logicallyincorrect/esp32-hid-switcher/src/HidReportMap.h

#pragma once
#include <stdint.h>
#include "PointerMode.h"
// One keyboard report ID, six keys plus modifiers. No shared live report value.
static uint8_t reportMap[] = {
  0x05,0x01, 0x09,0x06, 0xa1,0x01, 0x85,0x01,
  0x05,0x07, 0x19,0xe0, 0x29,0xe7, 0x15,0x00, 0x25,0x01,
  0x75,0x01, 0x95,0x08, 0x81,0x02,
  0x95,0x01, 0x75,0x08, 0x81,0x01,
  0x95,0x05, 0x75,0x01, 0x05,0x08, 0x19,0x01, 0x29,0x05, 0x91,0x02,
  0x95,0x01, 0x75,0x03, 0x91,0x01,
  0x95,0x06, 0x75,0x08, 0x15,0x00, 0x26,0xff,0x00,
  0x05,0x07, 0x19,0x00, 0x2a,0xff,0x00, 0x81,0x00, 0xc0,
#if HID_ABSOLUTE_POINTER
  // NanoKVM hid.GS2 layout, with report ID 2 for BLE alongside our keyboard.
  // Five buttons, absolute X/Y with explicit physical range, relative wheel.
  0x05,0x01,0x09,0x02,0xa1,0x01,0x85,0x02,0x09,0x01,0xa1,0x00,
  0x05,0x09,0x19,0x01,0x29,0x05,0x15,0x00,0x25,0x01,0x95,0x05,0x75,0x01,0x81,0x02,
  0x95,0x01,0x75,0x03,0x81,0x01,
  0x05,0x01,0x09,0x30,0x09,0x31,0x15,0x00,0x26,0xff,0x7f,0x35,0x00,0x46,0xff,0x7f,
  0x75,0x10,0x95,0x02,0x81,0x02,
  0x05,0x01,0x09,0x38,0x15,0x81,0x25,0x7f,0x35,0x00,0x45,0x00,0x75,0x08,0x95,0x01,0x81,0x06,0xc0,0xc0
#else
  // Standard relative mouse: eight buttons, signed 16-bit X/Y, wheel and pan.
  0x05,0x01,0x09,0x02,0xa1,0x01,0x85,0x02,0x09,0x01,0xa1,0x00,
  0x05,0x09,0x19,0x01,0x29,0x08,0x15,0x00,0x25,0x01,0x95,0x08,0x75,0x01,0x81,0x02,
  0x05,0x01,0x09,0x30,0x09,0x31,0x16,0x01,0x80,0x26,0xff,0x7f,0x75,0x10,0x95,0x02,0x81,0x06,
  0x09,0x38,0x15,0x81,0x25,0x7f,0x75,0x08,0x95,0x01,0x81,0x06,
  0x05,0x0c,0x0a,0x38,0x02,0x95,0x01,0x81,0x06,0xc0,0xc0
#endif
};
#if HID_ABSOLUTE_POINTER && !HID_ABSOLUTE_ONLY_TEST
// Own HID service and report map: never merge relative axes with absolute
// mouse buttons in one host HID device. Used for calibration and seamless-off.
static uint8_t relativeReportMap[] = {
  // Calibration uses a separate relative mouse; report 2 stays absolute.
  0x05,0x01,0x09,0x02,0xa1,0x01,0x85,0x03,0x09,0x01,0xa1,0x00,
  0x05,0x09,0x19,0x01,0x29,0x08,0x15,0x00,0x25,0x01,0x95,0x08,0x75,0x01,0x81,0x02,
  0x05,0x01,0x09,0x30,0x09,0x31,0x16,0x01,0x80,0x26,0xff,0x7f,0x75,0x10,0x95,0x02,0x81,0x06,
  0x09,0x38,0x15,0x81,0x25,0x7f,0x75,0x08,0x95,0x01,0x81,0x06,
  0x05,0x0c,0x0a,0x38,0x02,0x95,0x01,0x81,0x06,0xc0,0xc0
};
#endif
